jsheradin/hard-sector-punch/photos/IMG_20220701_180826.jpg

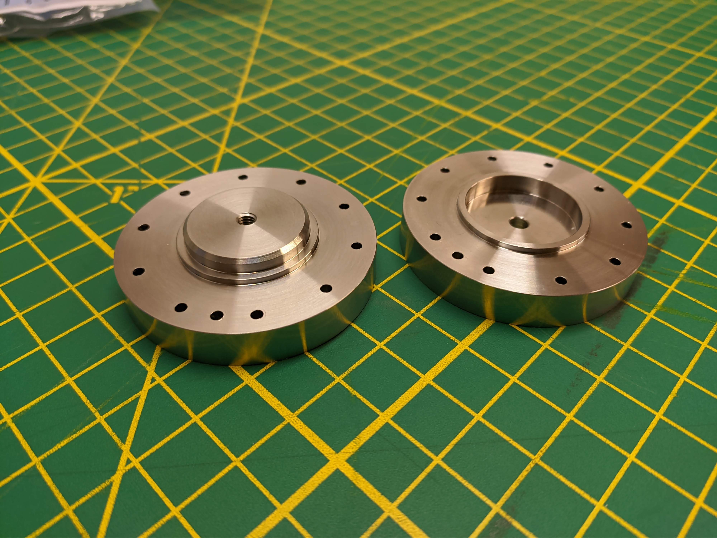
photos/IMG_20220701_180826.jpg
