jsheradin/hard-sector-punch/photos/IMG_20220701_190329.jpg

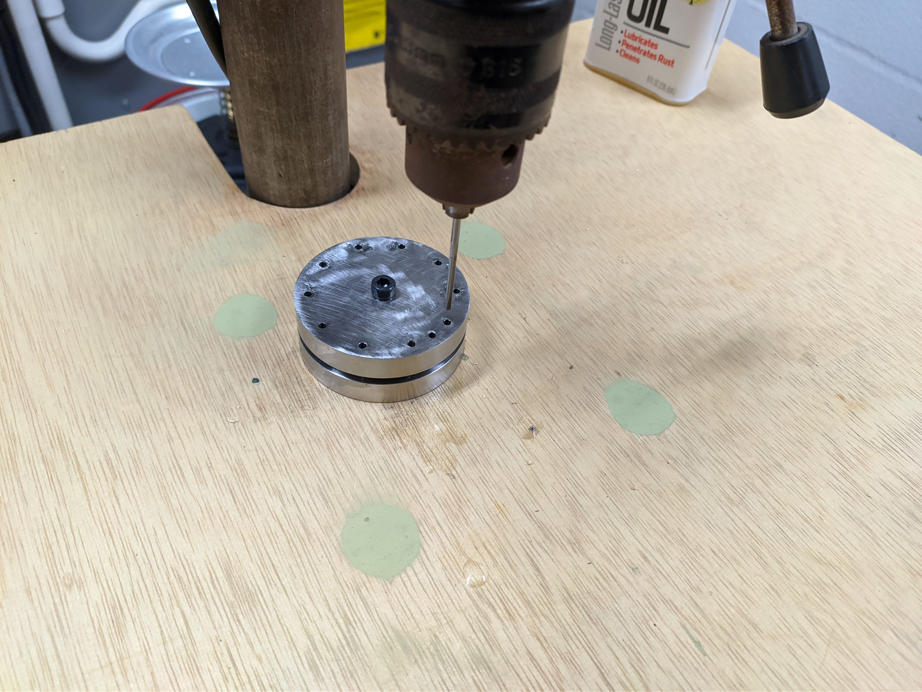
photos/IMG_20220701_190329.jpg
