jsheradin/hard-sector-punch/photos/IMG_20220701_205026.jpg

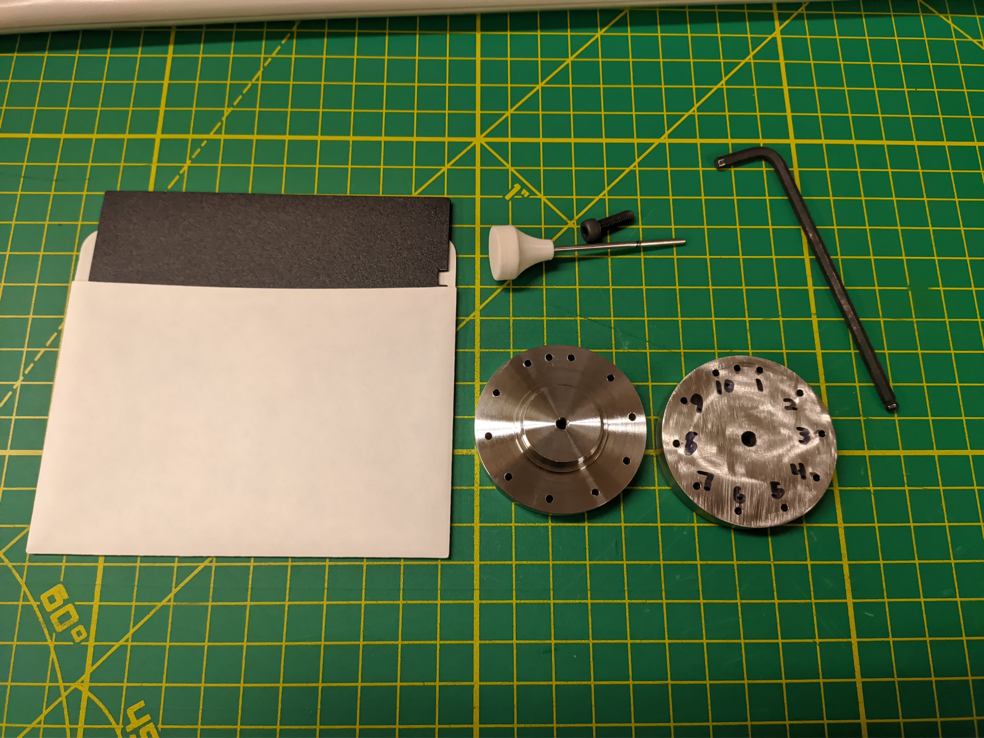
photos/IMG_20220701_205026.jpg
