jsheradin/hard-sector-punch/photos/IMG_20220701_205119.jpg

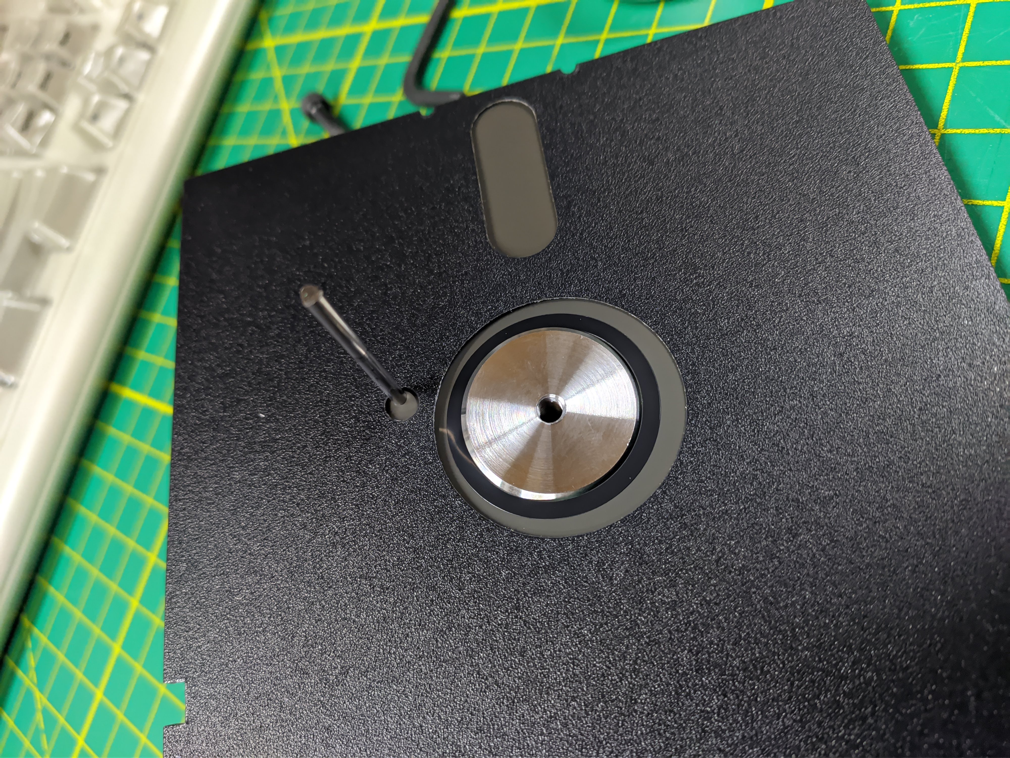
photos/IMG_20220701_205119.jpg
