jsheradin/hard-sector-punch/photos/IMG_20220701_205152.jpg

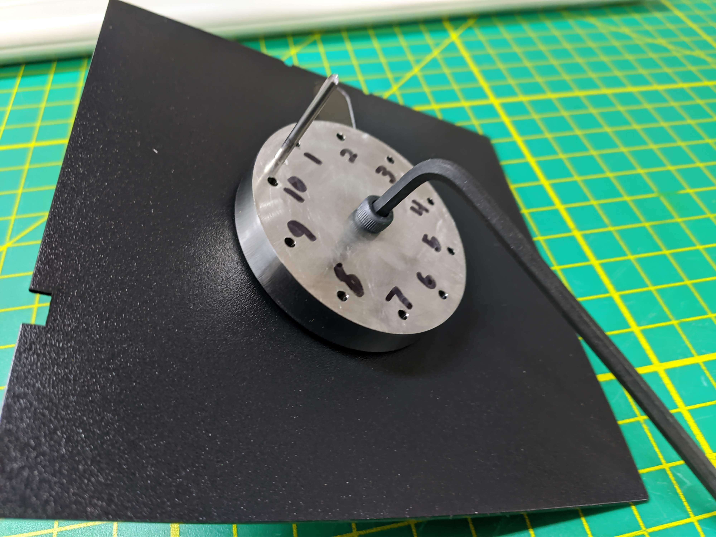
photos/IMG_20220701_205152.jpg
