jsheradin/hard-sector-punch/photos/IMG_20220701_205232.jpg

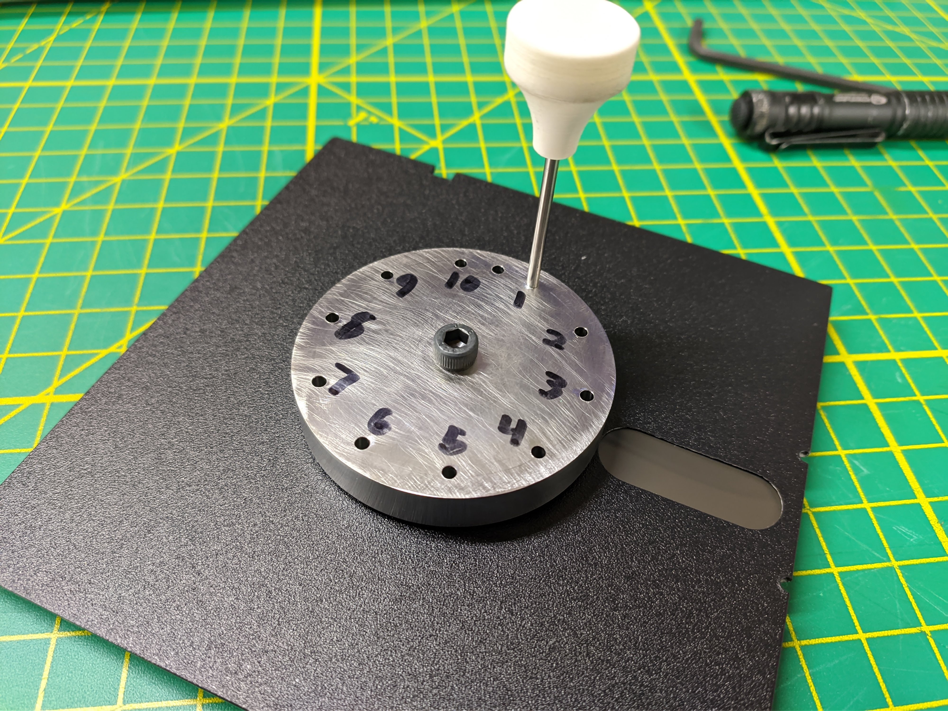
photos/IMG_20220701_205232.jpg
