jsheradin/hard-sector-punch/photos/IMG_20220701_205752.jpg

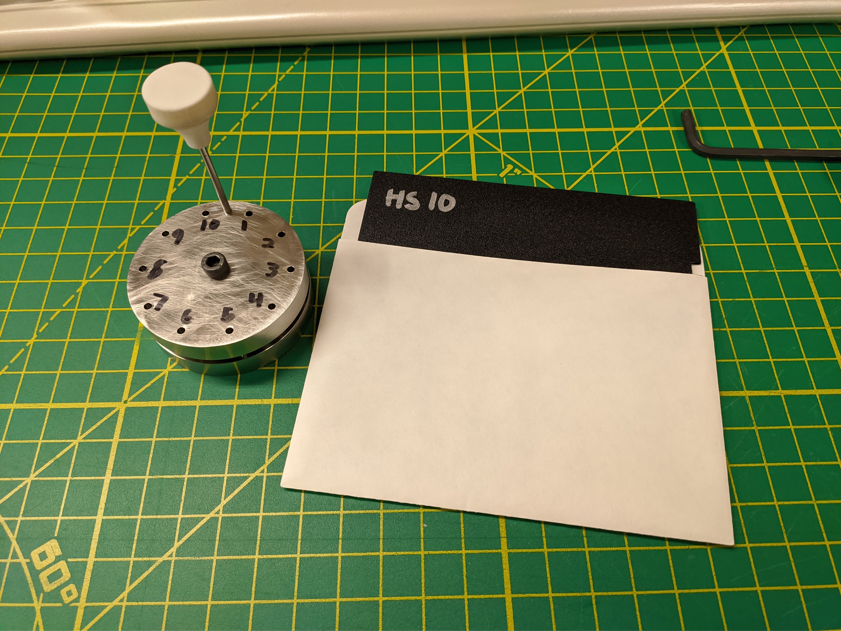
photos/IMG_20220701_205752.jpg
